MALITHA929/Automated-IoT-Smart-Water-Meter/Final product images/WhatsApp Image 2026-07-29 at 1.20.57 PM (1).jpeg

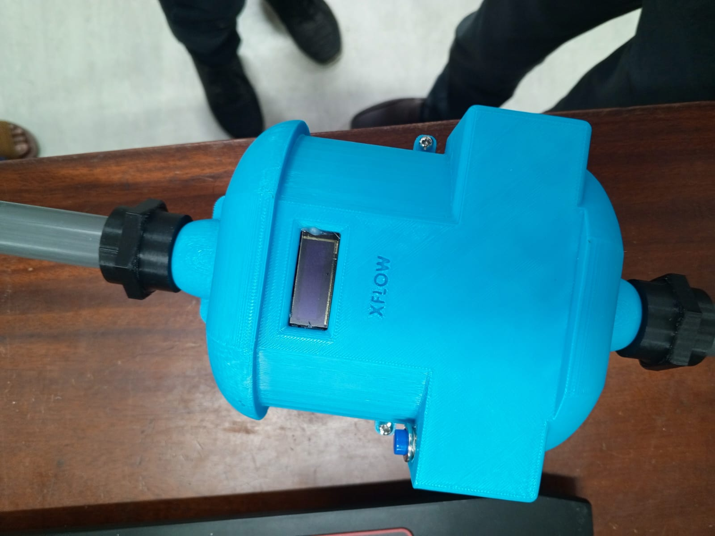
Final product images/WhatsApp Image 2026-07-29 at 1.20.57 PM (1).jpeg
